MiniAiLive/Physical-Access-Control-System/Firmware/RV1108/Setting/verifyfaceform.cpp

#include "verifyfaceform.h"
#include "ui_passcodeform.h"
#include "base.h"
#include "shared.h"
#include "uitheme.h"
#include "stringtable.h"
#include "engineparam.h"
#include "camerasurface.h"
#include "camera_api.h"
#include "mainwindow.h"
#include "rokthread.h"
#include "alertdlg.h"
#include "lcdtask.h"
#include "drv_gpio.h"
#include "faceengine.h"
#include "soundbase.h"
#include "playthread.h"
#include "my_lang.h"
#include "FaceRetrievalSystem.h"
#include "msg.h"
#include "rk_fb.h"
#include "facerecogtask.h"
#include "DBManager.h"
#include "menuform.h"
#include "cardrecogtask.h"
#include "i2cbase.h"
#include "uarttask.h"
#include "settings.h"

#include <QtGui>
#include <QLabel>
#include <unistd.h>

#define SCENE_SHOW_TIME    1000

extern int g_iMinSize;

VerifyFaceForm::VerifyFaceForm(QGraphicsView *pView, FormBase* pParentForm)
                               : FormBase(pView, pParentForm)
{
    SetupUI();

    m_iUIWaiting = 0;
    m_iOldMsg = -1;
    m_rResetTime = 0;
    m_rClickTime = 0;
    m_iCounter = 0;
    m_pFaceRecogTask = NULL;
    m_pCardRecogTask = NULL;
    m_iCurScene = SCENE_NONE;
    ResetButtons();

    setAutoDelete(false);

    connect(this, SIGNAL(SigBack(int, int)), this, SLOT(GotoBack(int, int)));
}

VerifyFaceForm::~VerifyFaceForm()
{
    SendGlobalMsg(MSG_VERIFY, VF_END, 0, 0);
    OnStop();
    delete ui;
    ui = NULL;
}

void VerifyFaceForm::StartVerify()
{
#if (AUTO_TEST == 1)
    qDebug() << "[Call]" << this << __FUNCTION__;
#endif

    FormBase::OnStart(0);

    g_xSS.iVerifyFlag = 1;
    g_xSS.rVerifyLoopTime = Now();
    m_iTimer = startTimer(500);
    QThreadPool::globalInstance()->start(this);
}
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
